aniva/theperfectkitebar/hardware/swivel/sheeting_rope_4mm/bearing_ZR51103/swivel-cap/variant_4/swivel-cap_sls.png

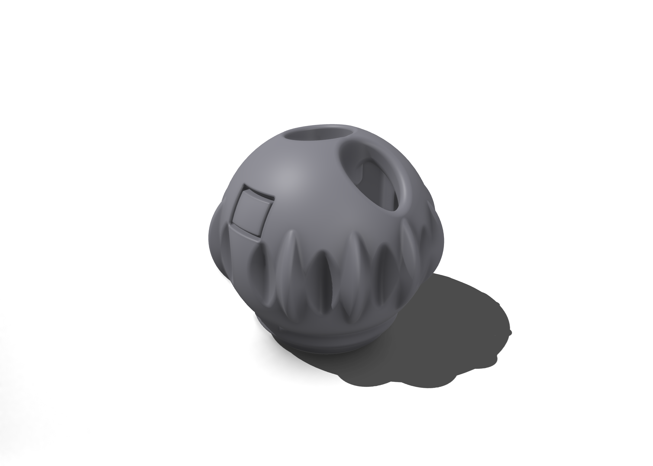
hardware/swivel/sheeting_rope_4mm/bearing_ZR51103/swivel-cap/variant_4/swivel-cap_sls.png
