aniva/theperfectkitebar/hardware/trim/sheeting_rope_4mm/front_line_1.4mm/safety_stopper/variant_3/line_stopper_14_mjf.png

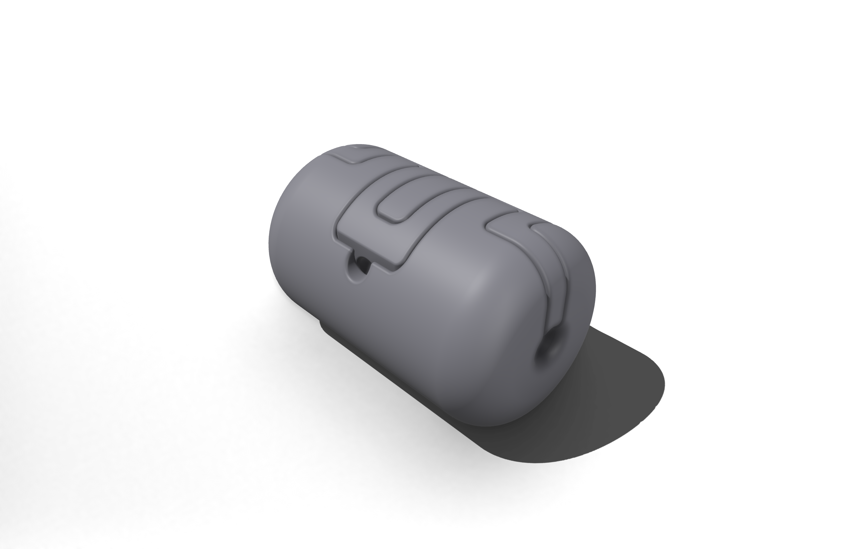
hardware/trim/sheeting_rope_4mm/front_line_1.4mm/safety_stopper/variant_3/line_stopper_14_mjf.png
