aniva/theperfectkitebar/images/bar_drill_01.jpeg

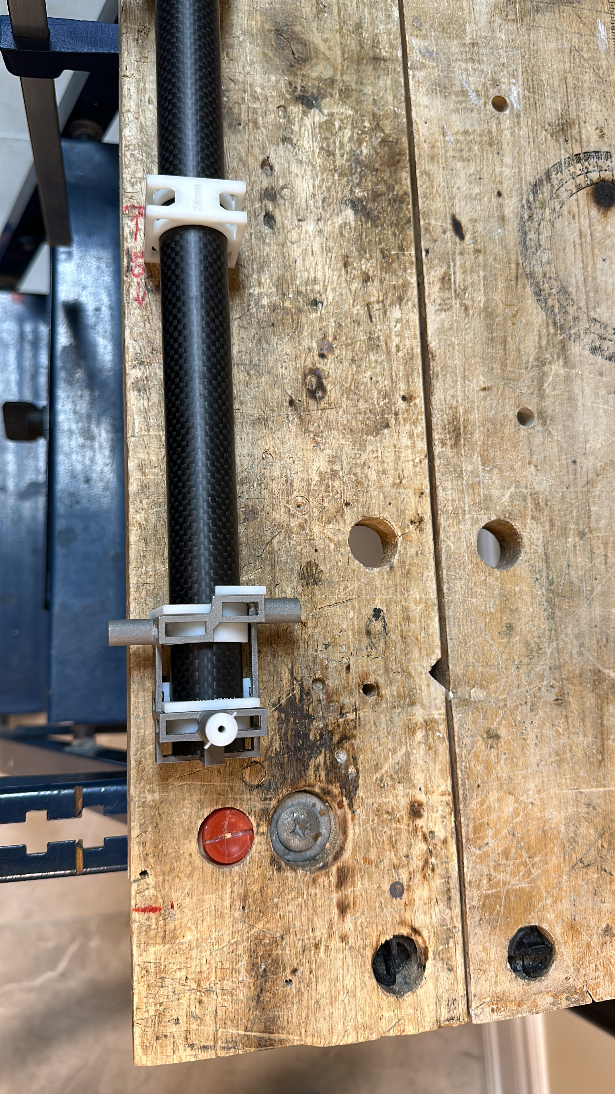
images/bar_drill_01.jpeg
