aniva/theperfectkitebar/images/bar_in_action_01.png

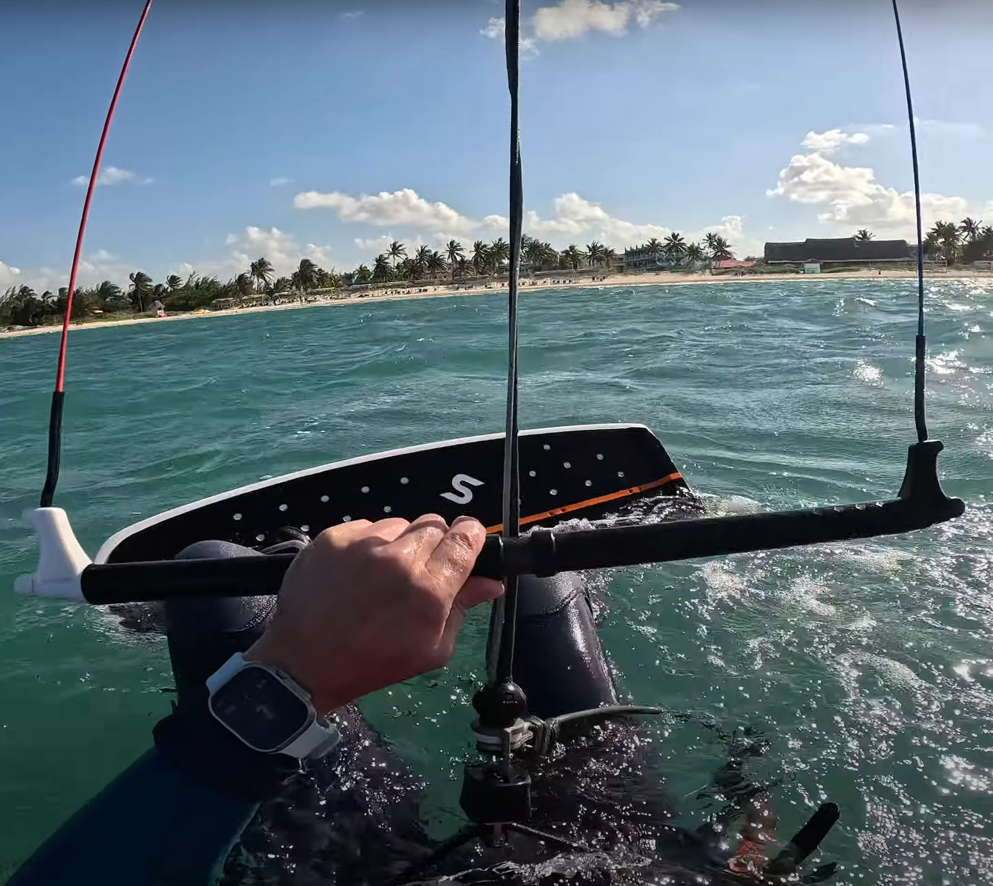
images/bar_in_action_01.png
