aniva/theperfectkitebar/images/jlc3dp_warning.jpeg

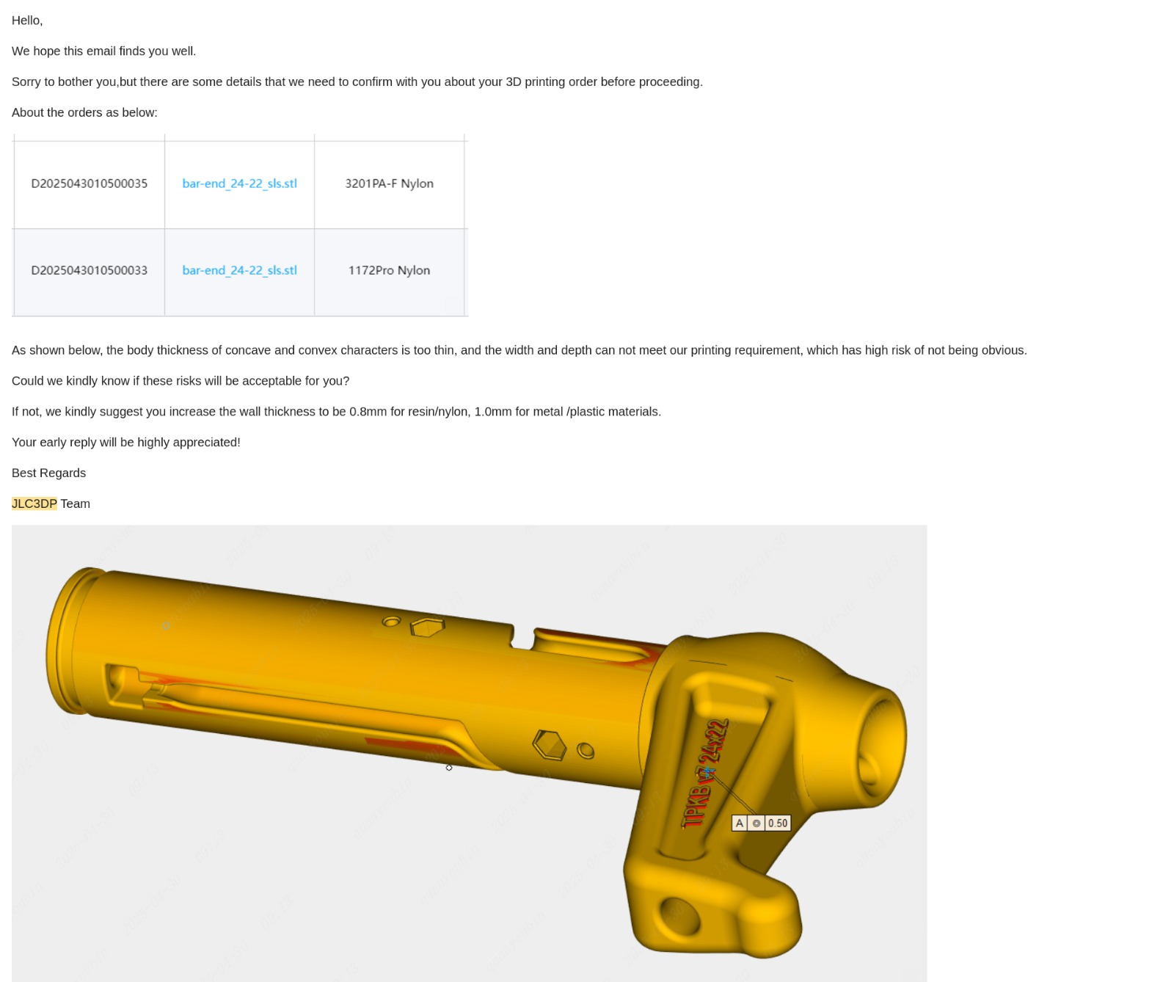
images/jlc3dp_warning.jpeg
