aniva/theperfectkitebar/images/temp_bar_svg_01.png

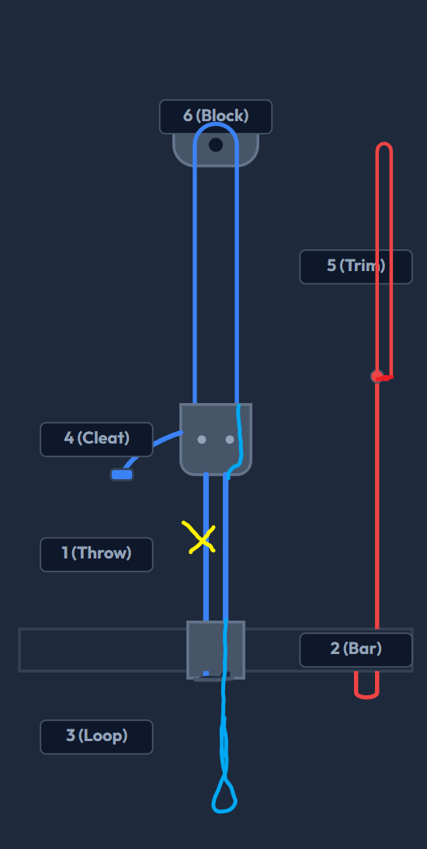
images/temp_bar_svg_01.png
