aniva/theperfectkitebar/hardware/swivel/sheeting_rope_4mm/bearing_ZR51103/swivel_housing_and_shaft/variant_4/swivel-shaft_17x3x9_slm.step

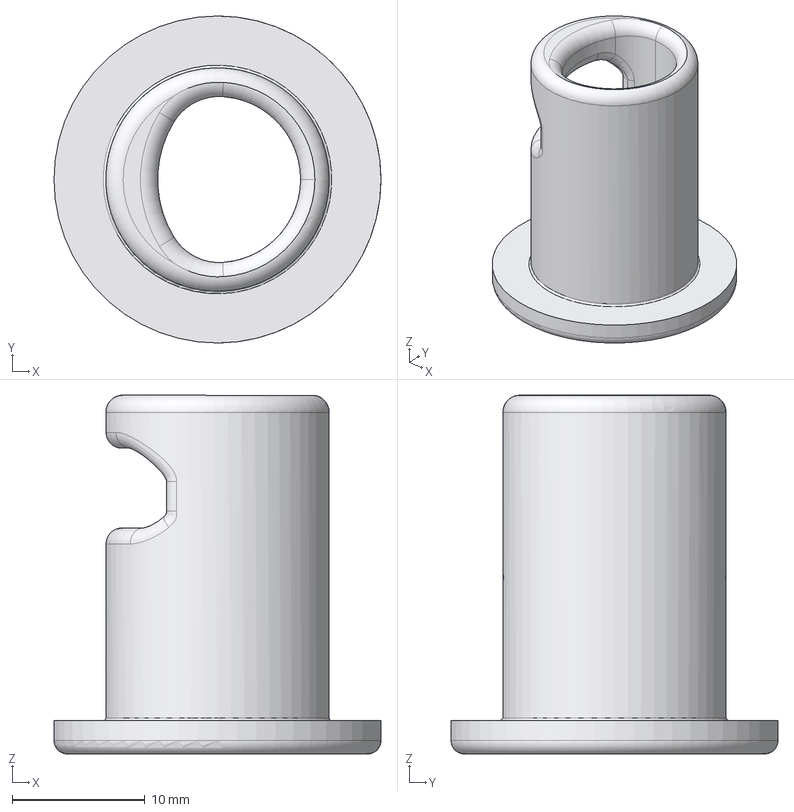
[picture p46: CAD file, 2025-06-20]
hardware/swivel/sheeting_rope_4mm/bearing_ZR51103/swivel_housing_and_shaft/variant_4/swivel-shaft_17x3x9_slm.step
24.6 x 24.6 x 27.0 mm
print checks
LILY_51103_PART4 x 14
LILY_51103_PART3
LILY_51103_PART2
LILY_51103_PART1
