aniva/theperfectkitebar/hardware/tools/sewing/SINGER_44xx/presser_foot_1.4mm_line_sla.step

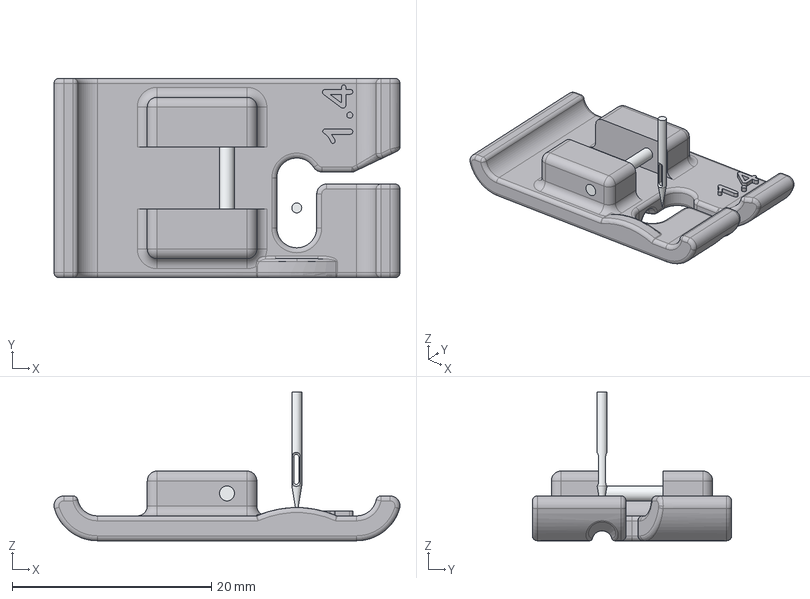
[picture p47: CAD file, 2025-06-01]
hardware/tools/sewing/SINGER_44xx/presser_foot_1.4mm_line_sla.step
34.7 x 20.0 x 14.9 mm
