aniva/theperfectkitebar/hardware/tools/sewing/SINGER_44xx/presser_foot_1.7mm_line_sla.step

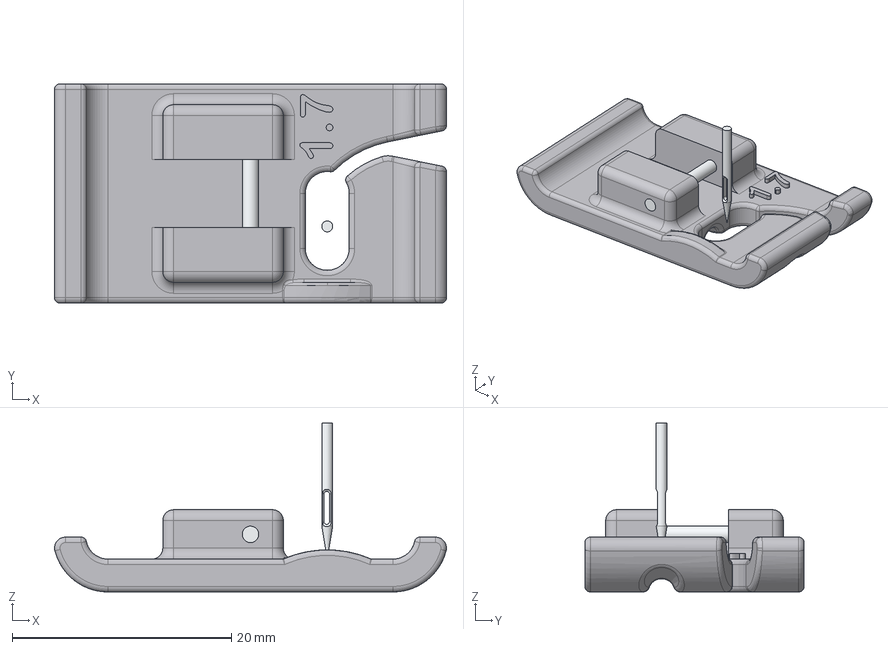
[picture p48: CAD file, 2025-06-01]
hardware/tools/sewing/SINGER_44xx/presser_foot_1.7mm_line_sla.step
35.7 x 20.0 x 15.4 mm
